cyrusbuilt/CLController/include/RelayMap.h

#ifndef _RELAY_MAP_H
#define _RELAY_MAP_H

// Pin definitions on the MCP23017
#define GPA0 0
#define GPA1 1
#define GPA2 2
#define GPA3 3
#define GPA4 4
#define GPA5 5
#define GPA6 6
#define GPA7 7
#define GPB0 8
#define GPB1 9
#define GPB2 10
#define GPB3 11
#define GPB4 12
#define GPB5 13
#define GPB6 14
#define GPB7 15

// Port A relay addresses 
#define PORTA_RELAY_1 GPA0
#define PORTA_RELAY_2 GPA1
#define PORTA_RELAY_3 GPA2
#define PORTA_RELAY_4 GPA3
#define PORTA_RELAY_5 GPA4
#define PORTA_RELAY_6 GPA7
#define PORTA_RELAY_7 GPA6
#define PORTA_RELAY_8 GPA5

// Port B relay addresses
#define PORTB_RELAY_1 GPB0
#define PORTB_RELAY_2 GPB1
#define PORTB_RELAY_3 GPB2
#define PORTB_RELAY_4 GPB3
#define PORTB_RELAY_5 GPB4
#define PORTB_RELAY_6 GPB7
#define PORTB_RELAY_7 GPB6
#define PORTB_RELAY_8 GPB5

#endif
